PrillBlizzard/Laser_Game_LTE-M/CR/Img/LAS.png

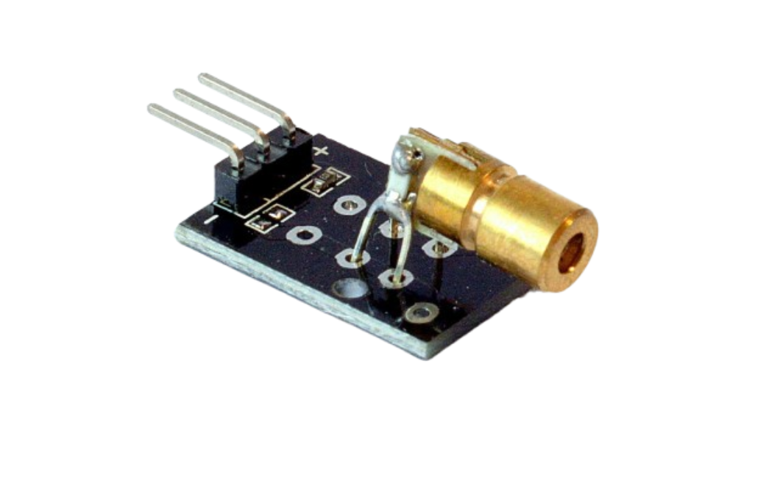
CR/Img/LAS.png
