PrillBlizzard/Laser_Game_LTE-M/CR/Img/LAS_reicv.png

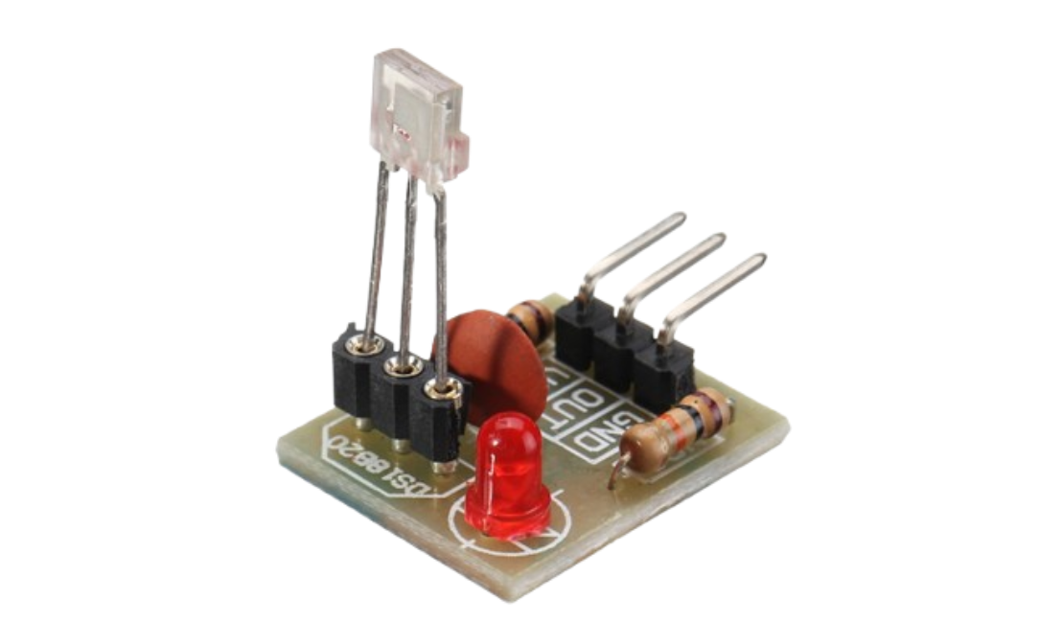
CR/Img/LAS_reicv.png
