PrillBlizzard/Laser_Game_LTE-M/CR/Img/Pres_RGB-LED_SK6812.png

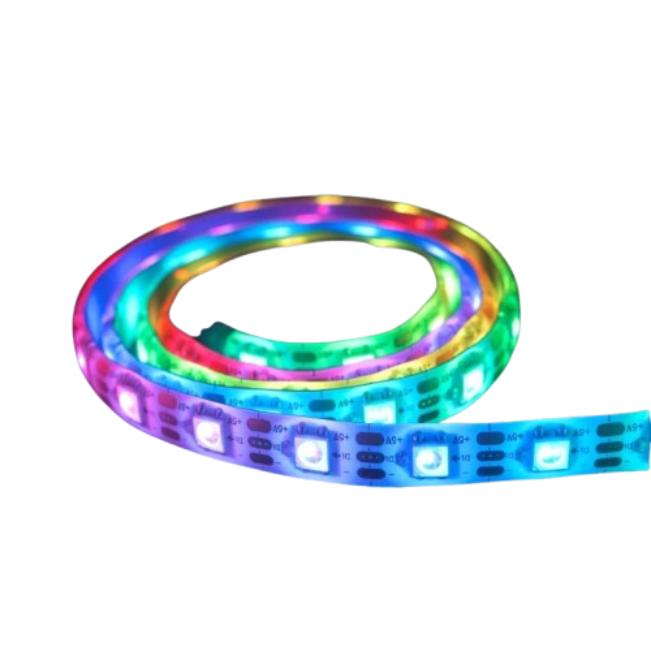
CR/Img/Pres_RGB-LED_SK6812.png
